vives-projectweek-2022/LannoLeave/firmware/docs/Sphinx/source/api/define_helper__funcs__var_8hpp_1a3ef3792ea0669dd940571f6674581818.rst

.. _exhale_define_helper__funcs__var_8hpp_1a3ef3792ea0669dd940571f6674581818:

Define PRINT_A
==============

- Defined in :ref:`file__home_joey_Documents_School_2022_Projectweek_Lannooleaf_firmware_helpers_include_helper_funcs_var.hpp`

Define Documentation
--------------------

.. doxygendefine:: PRINT_A
   :project: Lannooleaf firmware
