vives-projectweek-2022/LannoLeave/firmware/docs/Sphinx/source/api/classLannooleaf_1_1I2c__slave.rst

.. _exhale_class_classLannooleaf_1_1I2c__slave:

Class I2c_slave
===============

- Defined in :ref:`file__home_joey_Documents_School_2022_Projectweek_Lannooleaf_firmware_helpers_include_i2c_slave.h`

Class Documentation
-------------------

.. doxygenclass:: Lannooleaf::I2c_slave
   :project: Lannooleaf firmware
   :members:
   :protected-members:
   :undoc-members:
