vives-projectweek-2022/LannoLeave/firmware/docs/Sphinx/source/api/define_helper__funcs__var_8h_1a1630d697270d94a6c16d638197bfad02.rst

.. _exhale_define_helper__funcs__var_8h_1a1630d697270d94a6c16d638197bfad02:

Define I2C_CONTOLLER_PLACEHOLDER_ADDRESS
========================================

- Defined in :ref:`file__home_joey_Documents_School_2022_Projectweek_Lannooleaf_firmware_helpers_include_helper_funcs_var.h`

Define Documentation
--------------------

.. doxygendefine:: I2C_CONTOLLER_PLACEHOLDER_ADDRESS
   :project: Lannooleaf firmware
