vives-projectweek-2022/LannoLeave/firmware/docs/Sphinx/source/api/define_helper__funcs__var_8h_1ab4553be4db9860d940f81d7447173b2f.rst

.. _exhale_define_helper__funcs__var_8h_1ab4553be4db9860d940f81d7447173b2f:

Define LED_PIN
==============

- Defined in :ref:`file__home_joey_Documents_School_2022_Projectweek_Lannooleaf_firmware_helpers_include_helper_funcs_var.h`

Define Documentation
--------------------

.. doxygendefine:: LED_PIN
   :project: Lannooleaf firmware
