vives-projectweek-2022/LannoLeave/firmware/docs/Sphinx/source/api/define_helper__funcs__var_8h_1ab912078ca31ad64a455ad2b9c04c34e1.rst

.. _exhale_define_helper__funcs__var_8h_1ab912078ca31ad64a455ad2b9c04c34e1:

Define LED_LENGTH
=================

- Defined in :ref:`file__home_joey_Documents_School_2022_Projectweek_Lannooleaf_firmware_helpers_include_helper_funcs_var.h`

Define Documentation
--------------------

.. doxygendefine:: LED_LENGTH
   :project: Lannooleaf firmware
