vives-projectweek-2022/LannoLeave/firmware/docs/Sphinx/source/api/define_helper__funcs__var_8h_1ad61844ab25ea35139950e67e9693bc9f.rst

.. _exhale_define_helper__funcs__var_8h_1ad61844ab25ea35139950e67e9693bc9f:

Define PRINT
============

- Defined in :ref:`file__home_joey_Documents_School_2022_Projectweek_Lannooleaf_firmware_helpers_include_helper_funcs_var.h`

Define Documentation
--------------------

.. doxygendefine:: PRINT
   :project: Lannooleaf firmware
