vives-projectweek-2022/LannoLeave/firmware/docs/Sphinx/source/api/file__home_joey_Documents_School_2022_Projectweek_Lannooleaf_firmware_helpers_include_i2c_slave.h.rst

.. _file__home_joey_Documents_School_2022_Projectweek_Lannooleaf_firmware_helpers_include_i2c_slave.h:

File i2c_slave.h
================

|exhale_lsh| :ref:`Parent directory <dir__home_joey_Documents_School_2022_Projectweek_Lannooleaf_firmware_helpers_include>` (``/home/joey/Documents/School_2022/Projectweek/Lannooleaf/firmware/helpers/include``)

.. |exhale_lsh| unicode:: U+021B0 .. UPWARDS ARROW WITH TIP LEFTWARDS

Singelton class to use ri pi pico as i2c slave. 

.. contents:: Contents
   :local:
   :backlinks: none

Definition (``/home/joey/Documents/School_2022/Projectweek/Lannooleaf/firmware/helpers/include/i2c_slave.h``)
-------------------------------------------------------------------------------------------------------------

Detailed Description
--------------------

Joey De Smet (Joey@de-smet.org) 

0.1 

2022-05-04

Copyright 2022 Joey De Smet

Licensed under the Apache License, Version 2.0 (the "License"); you may not use this file except in compliance with the License. You may obtain a copy of the License at    http://www.apache.org/licenses/LICENSE-2.0
 Unless required by applicable law or agreed to in writing, software distributed under the License is distributed on an "AS IS" BASIS, WITHOUT WARRANTIES OR CONDITIONS OF ANY KIND, either express or implied. See the License for the specific language governing permissions and limitations under the License. 

Includes
--------

- ``array``

- ``hardware/i2c.h``

- ``helper_funcs_var.h`` (:ref:`file__home_joey_Documents_School_2022_Projectweek_Lannooleaf_firmware_helpers_include_helper_funcs_var.h`)

- ``i2c_slave_lib.h``

- ``pico/stdlib.h``

- ``pico/util/queue.h``

- ``queue``

- ``stdint.h``

Included By
-----------

- :ref:`file__home_joey_Documents_School_2022_Projectweek_Lannooleaf_firmware_helpers_i2c_slave.cpp`

- :ref:`file__home_joey_Documents_School_2022_Projectweek_Lannooleaf_firmware_Lannooleaf_include_leaf.h`

- :ref:`file__home_joey_Documents_School_2022_Projectweek_Lannooleaf_firmware_Lannooleaf_main.cpp`

Namespaces
----------

- :ref:`namespace_Lannooleaf`

Classes
-------

- :ref:`exhale_class_classLannooleaf_1_1I2c__slave`
