vives-projectweek-2022/LannoLeave/hardware/shape/shape tilings.png

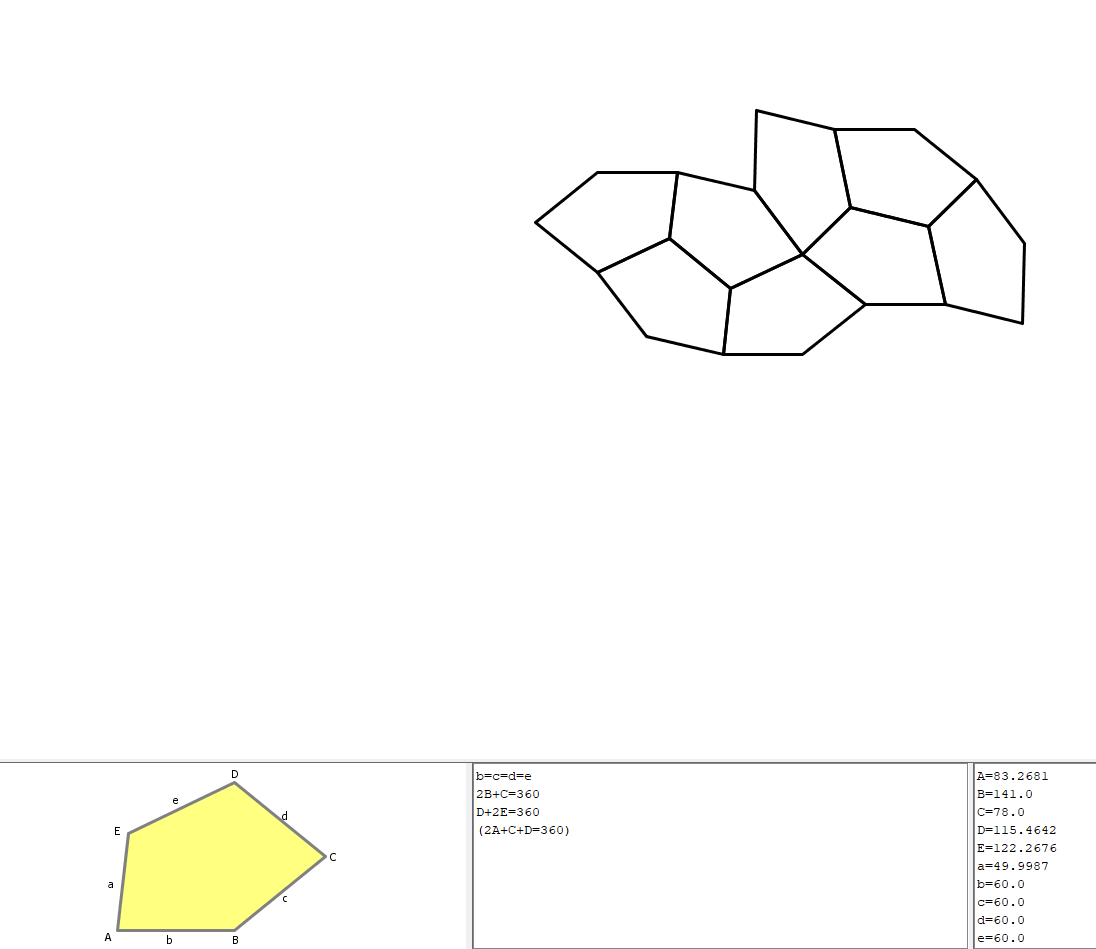
hardware/shape/shape tilings.png
