vives-projectweek-2022/LannoLeave/hardware/shape/tiling 2.png

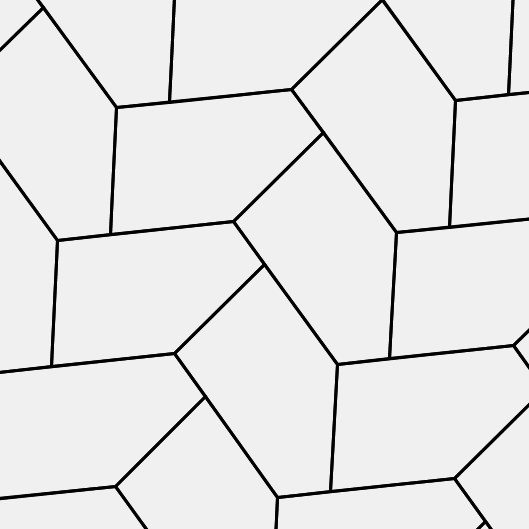
hardware/shape/tiling 2.png
