vives-projectweek-2022/LannoLeave/img/leave.png

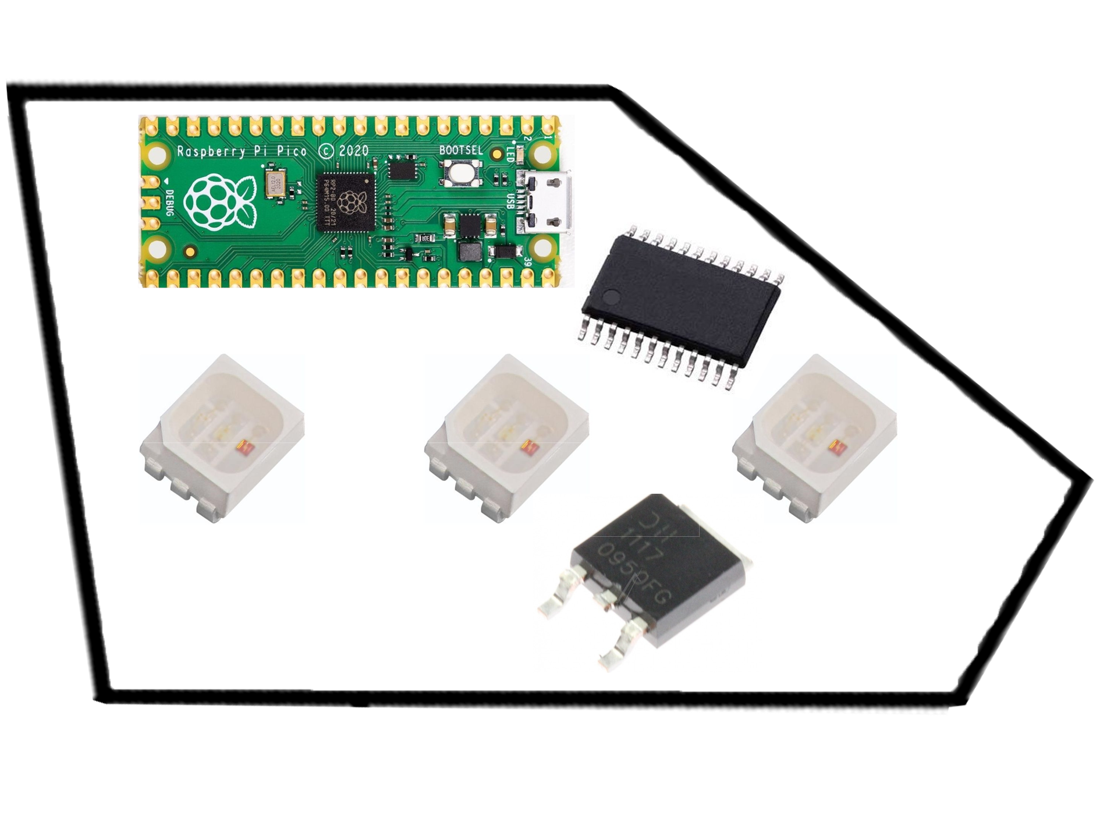
img/leave.png
