vives-projectweek-2022/LannoLeave/presentation/Diagram.png

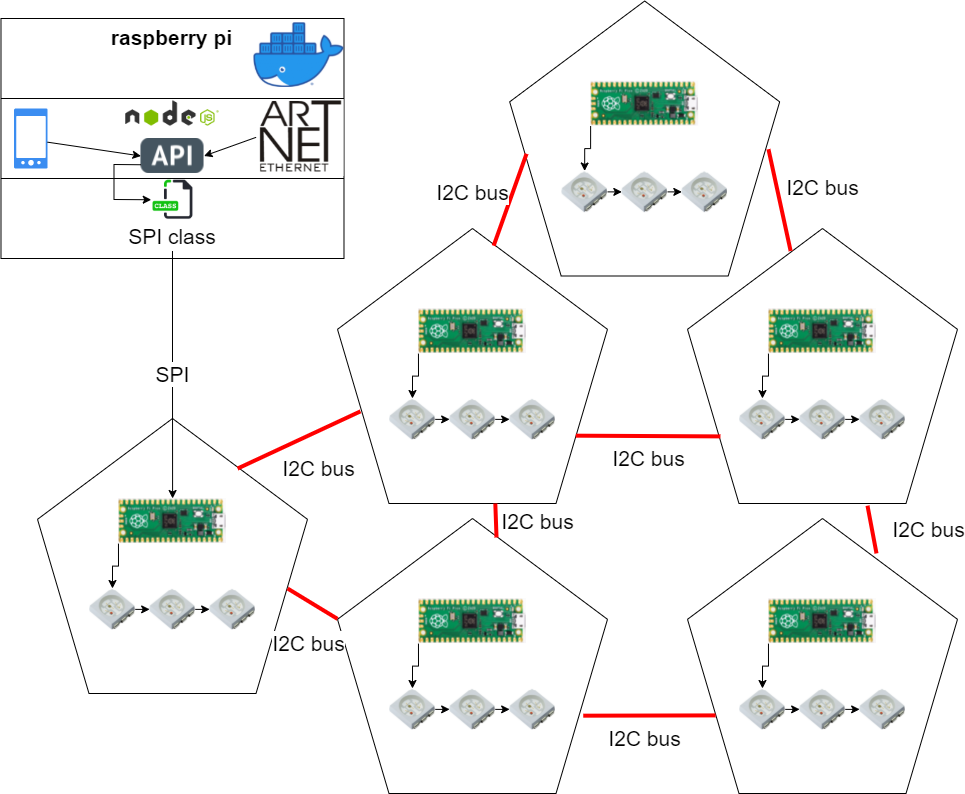
presentation/Diagram.png
