vives-projectweek-2022/LannoLeave/presentation/presentation1.jpg

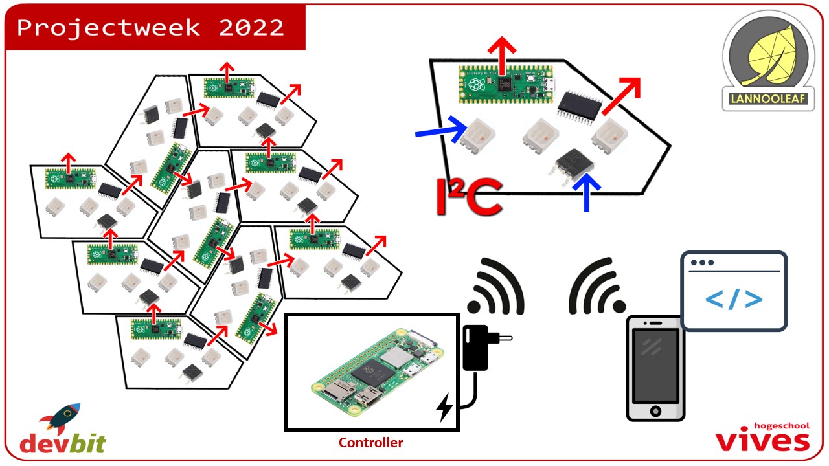
presentation/presentation1.jpg
