vives-projectweek-2022/LannoLeave/software/api/uploads/SpongeBob.png

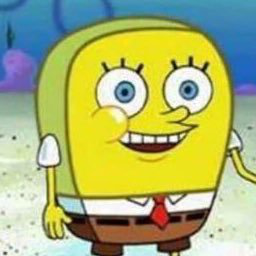
software/api/uploads/SpongeBob.png
