vives-projectweek-2022/LannoLeave/hardware/shape/tiles_school_measurement.jpg

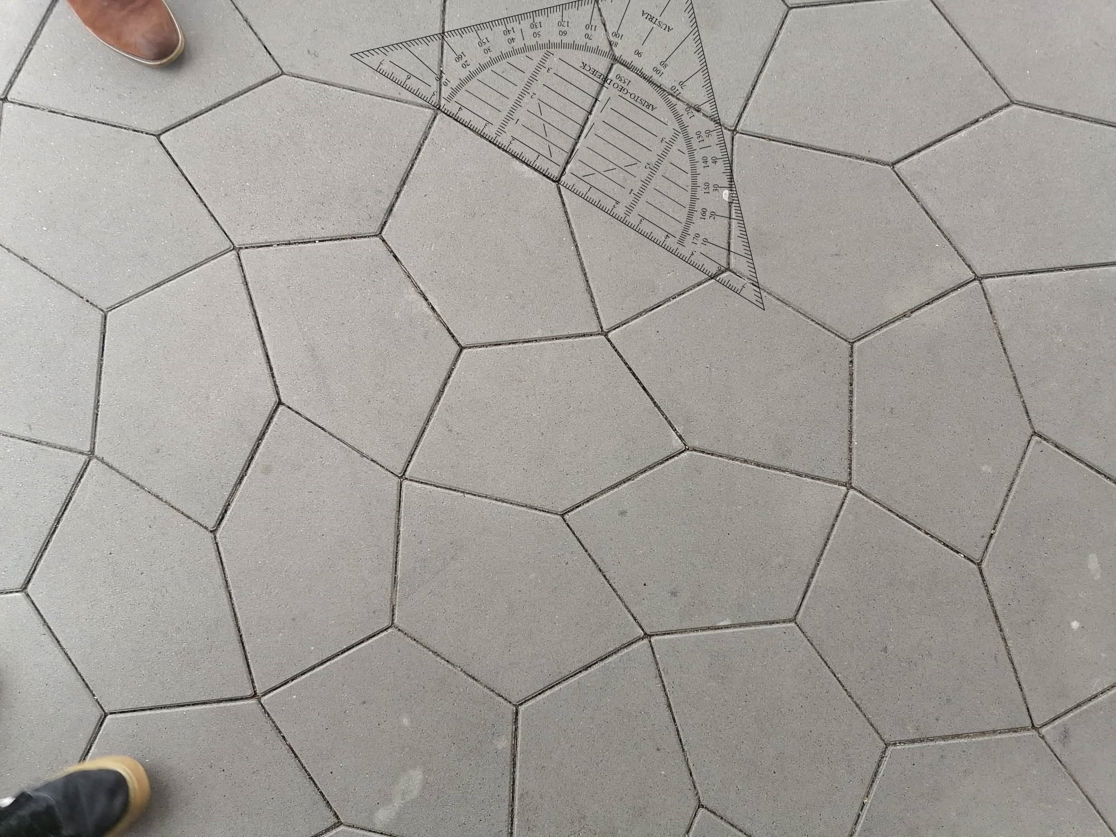
hardware/shape/tiles_school_measurement.jpg
